parth-20-07/Smart-Farm-Network/Gateway Server/Display Files/Rendered Images/Boot Screen.png

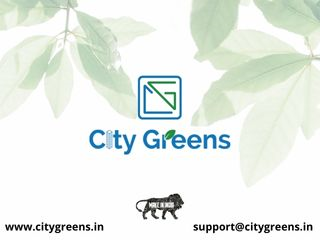
Gateway Server/Display Files/Rendered Images/Boot Screen.png
