parth-20-07/Smart-Farm-Network/Gateway Server/Display Files/Rendered Images/Configuration Screen.png

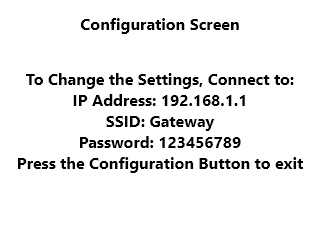
Gateway Server/Display Files/Rendered Images/Configuration Screen.png
