parth-20-07/Smart-Farm-Network/Gateway Server/Display Files/Rendered Images/Data Update Page.png

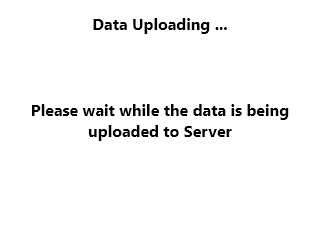
Gateway Server/Display Files/Rendered Images/Data Update Page.png
