parth-20-07/Smart-Farm-Network/Sensor Node/Firmware/include/Device_Configration.h

#ifndef Device_Configuration_h
#define Device_Configuration_h

/* -------------------------------------------------------------------------- */
/*                         BASIC DEVICE CONFIGURATION                         */
/* -------------------------------------------------------------------------- */
String DEVICE_NAME = "NODE - CITY GREENS";
#define BLE_UPDATE_TIME_COMMAND "time"   // Command recieved over ble to update time
#define BLE_UPDATE_SYNC_COMMAND "sync"   // Command to sync backlog data
#define BLE_UPDATE_SLEEP_COMMAND "sleep" // Command to go to sleep

/* -------------------------------------------------------------------------- */
/*                            SENSOR CONFIGURATION                            */
/* -------------------------------------------------------------------------- */
#define HTU21D_TEMP_HUMIDITY_SENSOR // Reference: https://learn.sparkfun.com/tutorials/htu21d-humidity-sensor-hookup-guide
#define MHZ19C_CO2_SENSOR           // Reference: https://github.com/strange-v/MHZ19/blob/master/examples/sw_get_values/sw_get_values.ino
#define BH1750_LUX_SENSOR           // Reference: https://randomnerdtutorials.com/arduino-bh1750-ambient-light-sensor/

/* -------------------------------------------------------------------------- */
/*                              RTC CONFIGURATION                             */
/* -------------------------------------------------------------------------- */
// #define DS3231_RTC
#define PCF8563_RTC

#endif
