parth-20-07/Smart-Farm-Network/Gateway Server/Firmware/include/OTA_Configuration.cpp

#include "Arduino.h"
#include <WiFi.h>
#include <HTTPClient.h>
#include <HTTPUpdate.h>
#include <WiFiClientSecure.h>
#include "cert.h"
#include "Variable_Declaration.h"

/* --------------------------- FUNCTION DEFINITION -------------------------- */
void update_firmware(void)
{
    Serial.println("Updating to new firmware");
    WiFiClientSecure client;
    client.setInsecure();
    client.setCACert(rootCACertificate);
    t_httpUpdate_return ret = httpUpdate.update(client, URL_fw_Bin);

    switch (ret)
    {
    case HTTP_UPDATE_FAILED:
        Serial.printf("HTTP_UPDATE_FAILD Error (%d): %s\n", httpUpdate.getLastError(), httpUpdate.getLastErrorString().c_str());
        break;

    case HTTP_UPDATE_NO_UPDATES:
        Serial.println("HTTP_UPDATE_NO_UPDATES");
        break;

    case HTTP_UPDATE_OK:
        Serial.println("HTTP_UPDATE_OK");
        break;
    }
}

uint8_t check_for_new_firmware(void)
{
    Serial.println("Checking for new Firmware");
    String payload;
    int httpCode;
    String fwurl = "";
    fwurl += URL_fw_Version;
    fwurl += "?";
    fwurl += String(rand());
    Serial.println(fwurl);
    WiFiClientSecure *client = new WiFiClientSecure;
    (*client).setInsecure();

    if (client)
    {
        client->setCACert(rootCACertificate);

        // Add a scoping block for HTTPClient https to make sure it is destroyed before WiFiClientSecure *client is
        HTTPClient https;

        if (https.begin(*client, fwurl))
        { // HTTPS
            Serial.print("[HTTPS] GET...\n");
            // start connection and send HTTP header
            delay(100);
            httpCode = https.GET();
            delay(100);
            if (httpCode == HTTP_CODE_OK)    // if version received
                payload = https.getString(); // save received version
            else
            {
                Serial.print("error in downloading version file:");
                Serial.println(httpCode);
            }
            https.end();
        }
        delete client;
    }

    if (httpCode == HTTP_CODE_OK) // if version received
    {
        payload.trim();
        if (payload.equals(firmware_version))
        {
            Serial.printf("\nDevice already on latest firmware version:%s\n", firmware_version);
            return 2;
        }
        else
        {
            Serial.println(payload);
            Serial.println("New firmware detected");
            return 1;
        }
    }
    return 0;
}
